PhenixRobotik/ivegotdapower-elec/simulation/first.asc

B1: bv; V=22
B2: bv; V=-20
M1: pmos; FDC5614P
M2: pmos; FDC5614P
Q1: pnp; 2N2907
Q2: pnp; 2N2907
Q3: pnp; 2N2907
Q4: pnp; 2N2907
R1: res; 10k
R2: res; 10k
R3: res; 100
R4: res; 10k
R5: res; 10k
Named nets: 0
.tran 0 10 0 0.1
